g0r3/esp8266-thermometer/thermometer/WeatherIcons.h

const unsigned char thermometer[350] PROGMEM = { /* 0X00,0X01,0X32,0X00,0X32,0X00, */
0X00,0X00,0X01,0XE0,0X00,0X00,0X00,0X00,0X00,0X07,0XF8,0X00,0X00,0X00,0X00,0X00,
0X1F,0XFE,0X00,0X00,0X00,0X00,0X00,0X1F,0XFE,0X00,0X00,0X00,0X00,0X00,0X3E,0X1F,
0X00,0X00,0X00,0X00,0X00,0X7C,0X0F,0X80,0X00,0X00,0X00,0X00,0X78,0X07,0X80,0X00,
0X00,0X00,0X00,0X78,0X07,0X80,0X00,0X00,0X00,0X00,0X78,0X07,0X80,0X00,0X00,0X00,
0X00,0X78,0X07,0X80,0X00,0X00,0X00,0X00,0X78,0X07,0X80,0X00,0X00,0X00,0X00,0X78,
0X07,0X80,0X00,0X00,0X00,0X00,0X78,0X07,0X80,0X00,0X00,0X00,0X00,0X78,0X07,0X80,
0X00,0X00,0X00,0X00,0X78,0X07,0X80,0X00,0X00,0X00,0X00,0X78,0X07,0X80,0X00,0X00,
0X00,0X00,0X78,0X07,0X80,0X00,0X00,0X00,0X00,0X79,0XE7,0X80,0X00,0X00,0X00,0X00,
0X79,0XE7,0X80,0X00,0X00,0X00,0X00,0X79,0XE7,0X80,0X00,0X00,0X00,0X00,0X79,0XE7,
0X80,0X00,0X00,0X00,0X00,0X79,0XE7,0X80,0X00,0X00,0X00,0X00,0X79,0XE7,0X80,0X00,
0X00,0X00,0X00,0X79,0XE7,0X80,0X00,0X00,0X00,0X00,0X79,0XE7,0X80,0X00,0X00,0X00,
0X00,0X79,0XE7,0X80,0X00,0X00,0X00,0X00,0X79,0XE7,0X80,0X00,0X00,0X00,0X00,0X79,
0XE7,0X80,0X00,0X00,0X00,0X00,0X79,0XE7,0X80,0X00,0X00,0X00,0X00,0XF9,0XE7,0XC0,
0X00,0X00,0X00,0X01,0XF1,0XE3,0XE0,0X00,0X00,0X00,0X03,0XE1,0XE1,0XF0,0X00,0X00,
0X00,0X03,0XC3,0XF0,0XF0,0X00,0X00,0X00,0X07,0X87,0XF8,0X78,0X00,0X00,0X00,0X07,
0X8F,0XFC,0X78,0X00,0X00,0X00,0X07,0X9F,0XFE,0X78,0X00,0X00,0X00,0X07,0X1F,0XFE,
0X38,0X00,0X00,0X00,0X07,0X1F,0XFE,0X38,0X00,0X00,0X00,0X07,0X1F,0XFE,0X38,0X00,
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
0X00,0X00,0X00,0X00,0X00,0X00,0X00,0X00,0X00,0X00,0X00,0X00,0X00,0X00,0X00,0X00,
0X00,0X00,0X00,0X00,0X00,0X00,0X00,0X00,0X00,0X00,0X00,0X00,0X00,0X00,0X00,0X00,
0X00,0X00,0X00,0X00,0X00,0X00,0X00,0X00,0X00,0X00,0X00,0X00,0X00,0X00,0X00,0X00,
0X00,0X00,};
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
